KIHestad/Ctrl-MC/Prototype2/SRC/DisplayHeadUnit_ESP32/README.md

Ctrl-MC logo

# Arduino Motorcycle Controller Software - PROTOTYPE 2

This is the second prototype from September 2025, for use with ESP32 WROOM 32 dev board. 
It is just for testing how to create a speedomenter and tachometer (rpm counter) using different kind of sensors.

Check here for more info: https://youtu.be/J_AsExU7qkA?si=yqhxXnDfag6Xr95b
