KIHestad/Ctrl-MC/Documents/Marketing Images/Keyboard_ver1.png

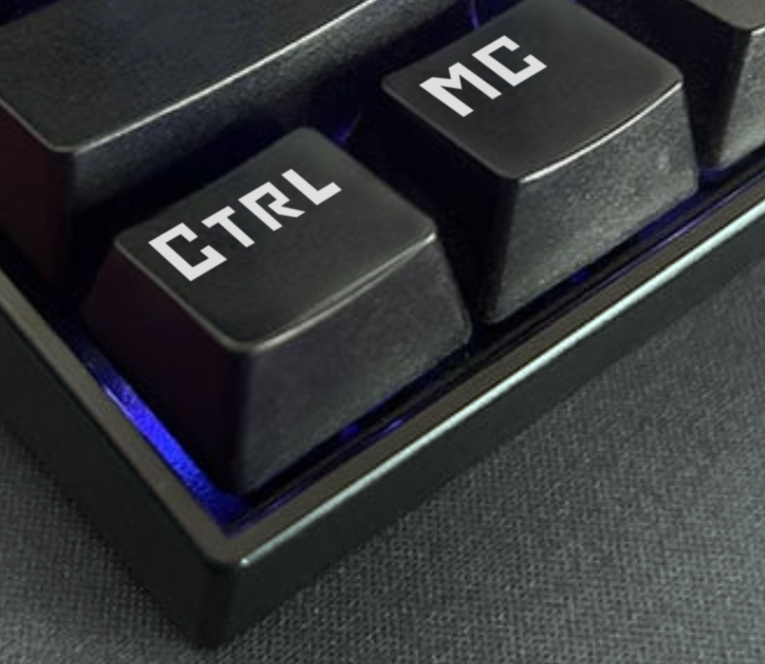
Documents/Marketing Images/Keyboard_ver1.png
