KIHestad/Ctrl-MC/Prototype4_8ch_spoc/Prototype4_8ch_spoc_SRC/_documents/documents/infineon-spoc-bts72220-4esa-datasheet-figure_37.png

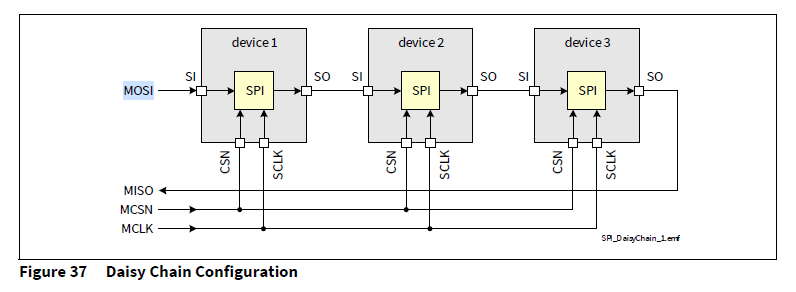
Prototype4_8ch_spoc/Prototype4_8ch_spoc_SRC/_documents/documents/infineon-spoc-bts72220-4esa-datasheet-figure_37.png
