KIHestad/Ctrl-MC/Prototype4_8ch_spoc/Prototype4_8ch_spoc_SRC/_documents/documents/infineon-spoc-bts72220-4esa-datasheet-figure_38.png

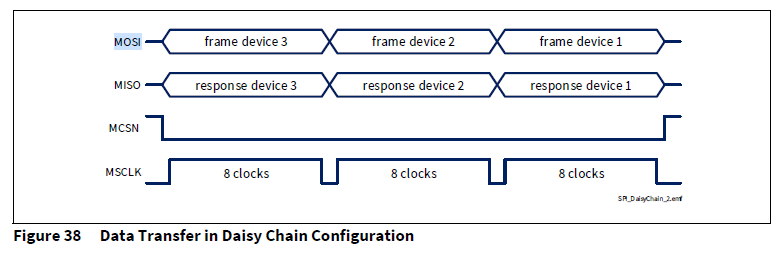
Prototype4_8ch_spoc/Prototype4_8ch_spoc_SRC/_documents/documents/infineon-spoc-bts72220-4esa-datasheet-figure_38.png
