KIHestad/Ctrl-MC/Ctrl-MC_DisplayUnit/include/Image.h

/***  Ctrl-MC // An open source Motorcycle Controller Arduino project by KI Hestad: https://github.com/KIHestad/Ctrl-MC  ***/

class Image {

    private:

        void image(const unsigned char img[], ImagePosition imgPos, uint8_t width, uint8_t height) {
            if (imgPos == imgPosMenuCenter)
                display.drawBitmap((DISPLAY_SCREEN_WIDTH/2)-(width/2), 3+25-(height/2), img, width, height, SSD1306_WHITE);
            else if (imgPos == imgPosCenter)
                display.drawBitmap((DISPLAY_SCREEN_WIDTH/2)-(width/2), (DISPLAY_SCREEN_HEIGHT/2)-(height/2), img, width, height, SSD1306_WHITE);
            else if (imgPos == imgPos2Left)
                display.drawBitmap(0, (DISPLAY_SCREEN_HEIGHT/2)-(height/2), img, width, height, SSD1306_WHITE);
            else if (imgPos == imgPos2Right)
                display.drawBitmap(DISPLAY_SCREEN_WIDTH-width, (DISPLAY_SCREEN_HEIGHT/2)-(height/2), img, width, height, SSD1306_WHITE);
            else if (imgPos == imgPos3Left)
                display.drawBitmap(((DISPLAY_SCREEN_WIDTH-35)/2)-(width/2), (DISPLAY_SCREEN_HEIGHT/2)-(height/2), img, width, height, SSD1306_WHITE);
            else if (imgPos == imgPos3RightTop)
                display.drawBitmap(DISPLAY_SCREEN_WIDTH-width, 0, img, width, height, SSD1306_WHITE);
            else if (imgPos == imgPos3RightBottom)
                display.drawBitmap(DISPLAY_SCREEN_WIDTH-width, DISPLAY_SCREEN_HEIGHT/2, img, width, height, SSD1306_WHITE);
        }

    public:
    
        void kiHestadLogo() {
            static const unsigned char PROGMEM img[] = {
                0xff, 0xff, 0xff, 0xff, 0xff, 0xff, 0xff, 0xff, 0xff, 0xff, 0xff, 0xff, 0xff, 0xff, 0xff, 0xff, 
                0xff, 0xff, 0xff, 0xff, 0xff, 0xff, 0xff, 0xff, 0xff, 0xff, 0xff, 0xff, 0xff, 0xff, 0xff, 0xff, 
                0xff, 0xff, 0xff, 0xff, 0xff, 0xff, 0xff, 0xff, 0xff, 0xff, 0xff, 0xff, 0xff, 0xff, 0xff, 0xff, 
                0xff, 0xff, 0xff, 0xff, 0xff, 0xff, 0xff, 0xe0, 0x07, 0xff, 0xff, 0xff, 0xff, 0xff, 0xff, 0xff, 
                0xff, 0xff, 0xff, 0xff, 0xff, 0xff, 0xfe, 0x00, 0x00, 0x7f, 0xff, 0xff, 0xff, 0xff, 0xff, 0xff, 
                0xff, 0xff, 0xff, 0xff, 0xff, 0xff, 0xf0, 0x1f, 0xf8, 0x1f, 0xff, 0xff, 0xff, 0xff, 0xff, 0xff, 
                0xff, 0xff, 0xff, 0xff, 0xff, 0xff, 0xc1, 0xff, 0xff, 0x03, 0xff, 0xff, 0xff, 0xff, 0xff, 0xff, 
                0xff, 0xff, 0xff, 0xff, 0xff, 0xff, 0x87, 0xdf, 0xff, 0xe1, 0xff, 0xff, 0xff, 0xff, 0xff, 0xff, 
                0xff, 0xff, 0xff, 0xff, 0xff, 0xfe, 0x1f, 0x8f, 0x3d, 0xf8, 0x7f, 0xff, 0xff, 0xff, 0xff, 0xff, 
                0xff, 0xff, 0xff, 0xff, 0xff, 0xfc, 0x7d, 0xcf, 0x3c, 0xfe, 0x3f, 0xff, 0xff, 0xff, 0xff, 0xff, 
                0xff, 0xff, 0xff, 0xff, 0xff, 0xf8, 0xf8, 0xc6, 0x38, 0xff, 0x1f, 0xff, 0xff, 0xff, 0xff, 0xff, 
                0xff, 0xff, 0xff, 0xff, 0xff, 0xf3, 0xfc, 0x42, 0x11, 0xcf, 0x8f, 0xff, 0xff, 0xff, 0xff, 0xff, 
                0xff, 0xff, 0xff, 0xff, 0xff, 0xe7, 0xfc, 0x00, 0x00, 0x8f, 0xc7, 0xff, 0xff, 0xff, 0xff, 0xff, 
                0xff, 0xff, 0xff, 0xff, 0xff, 0xcf, 0xfc, 0x0c, 0xc4, 0x0f, 0xe3, 0xff, 0xff, 0xff, 0xff, 0xff, 
                0xff, 0xff, 0xff, 0xff, 0xff, 0x9f, 0xfc, 0x7f, 0xfc, 0x0f, 0xf1, 0xff, 0xff, 0xff, 0xff, 0xff, 
                0xff, 0xff, 0xff, 0xff, 0xff, 0x1f, 0xfe, 0x7f, 0xff, 0xcf, 0xf8, 0xff, 0xff, 0xff, 0xff, 0xff, 
                0xff, 0xff, 0xff, 0xff, 0xff, 0x3f, 0xfe, 0xff, 0xff, 0xcf, 0xfc, 0xff, 0xff, 0xff, 0xff, 0xff, 
                0xff, 0xff, 0xff, 0xff, 0xfe, 0x7f, 0xff, 0xff, 0xff, 0xff, 0xfe, 0x7f, 0xff, 0xff, 0xff, 0xff, 
                0xff, 0xff, 0xff, 0xff, 0xfc, 0x7f, 0xf1, 0xff, 0xff, 0xef, 0xfe, 0x7f, 0xff, 0xff, 0xff, 0xff, 
                0xff, 0xff, 0xff, 0xff, 0xfc, 0xff, 0xe0, 0xff, 0xff, 0xc3, 0xff, 0x3f, 0xff, 0xff, 0xff, 0xff, 
                0xff, 0xff, 0xff, 0xff, 0xf8, 0xff, 0xe4, 0xff, 0xbf, 0xc3, 0xff, 0x3f, 0xff, 0xff, 0xff, 0xff, 
                0xff, 0xff, 0xff, 0xff, 0xf9, 0xff, 0xe7, 0xf1, 0x87, 0xf3, 0xff, 0x9f, 0xff, 0xff, 0xff, 0xff, 
                0xff, 0xff, 0xff, 0xff, 0xf9, 0xff, 0xe7, 0xc3, 0xc3, 0xf9, 0xff, 0x9f, 0xff, 0xff, 0xff, 0xff, 
                0xff, 0xff, 0xff, 0xff, 0xf3, 0xff, 0xe7, 0x8f, 0xf3, 0xf9, 0xff, 0x9f, 0xff, 0xff, 0xff, 0xff, 
                0xff, 0xff, 0xff, 0xff, 0xf3, 0xff, 0xe7, 0xff, 0xff, 0x93, 0xff, 0xcf, 0xff, 0xff, 0xff, 0xff, 
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
                0x00, 0x00, 0x00, 0x00, 0x00, 0x00, 0x00, 0x00, 0x00, 0x00, 0x00, 0x00, 0x00, 0x00
            };
            uint8_t width = 50;
            uint8_t height = 50;
            if (left) {
                uint8_t leftPosition = (DISPLAY_SCREEN_WIDTH/2)-6-width;
                display.drawBitmap(leftPosition, 3, img, width, height, SSD1306_INVERSE);
            } 
            if (right) {
                uint8_t leftPosition = (DISPLAY_SCREEN_WIDTH/2)+6;
                display.drawBitmap(leftPosition, 3, img, width, height, SSD1306_INVERSE);
            } 

        }
        
        void menuSelectIconConfirm(bool left, bool right) {
            static const unsigned char PROGMEM img[] = {
                // 'MenuCheckIconX', 19x19px
                0x20, 0x00, 0x80, 0x70, 0x01, 0xc0, 0xf8, 0x03, 0xe0, 0x7c, 0x07, 0xc0, 0x3e, 0x0f, 0x80, 0x1f, 
                0x1f, 0x00, 0x0f, 0xbe, 0x00, 0x07, 0xfc, 0x00, 0x03, 0xf8, 0x00, 0x01, 0xf0, 0x00, 0x03, 0xf8, 
                0x00, 0x07, 0xfc, 0x00, 0x0f, 0xbe, 0x00, 0x1f, 0x1f, 0x00, 0x3e, 0x0f, 0x80, 0x7c, 0x07, 0xc0, 
                0xf8, 0x03, 0xe0, 0x70, 0x01, 0xc0, 0x20, 0x00, 0x80
            };
            uint8_t width = 19;
            uint8_t height = 19;
            uint8_t y = 3 + 11;
            if (left) {
                uint8_t x = ((DISPLAY_SCREEN_WIDTH/2)-6-25)-(width/2);
                display.drawBitmap(x, y, img, width, height, SSD1306_WHITE);
            }
            if (right) {
                uint8_t x = ((DISPLAY_SCREEN_WIDTH/2)+6+25)-(width/2);
                display.drawBitmap(x, y, img, width, height, SSD1306_WHITE);
            }

        }

        void menuSelectIconReject(bool left, bool right) {
            static const unsigned char PROGMEM img[] = {
                // 'MenuCheckIconCheck', 19x18px
                0x00, 0x00, 0x80, 0x00, 0x01, 0xc0, 0x00, 0x03, 0xe0, 0x00, 0x03, 0xe0, 0x00, 0x07, 0xc0, 0x00, 
                0x0f, 0x80, 0x00, 0x1f, 0x00, 0x00, 0x1f, 0x00, 0x00, 0x3e, 0x00, 0x20, 0x7c, 0x00, 0x70, 0xf8, 
                0x00, 0xf8, 0xf8, 0x00, 0x7d, 0xf0, 0x00, 0x3f, 0xe0, 0x00, 0x1f, 0xc0, 0x00, 0x0f, 0xc0, 0x00, 
                0x07, 0x80, 0x00, 0x03, 0x00, 0x00
            };
            uint8_t width = 19;
            uint8_t height = 18;
            uint8_t y = 3 + 11;
            if (left) {
                uint8_t x = ((DISPLAY_SCREEN_WIDTH/2)-6-25)-(width/2);
                display.drawBitmap(x, y, img, width, height, SSD1306_WHITE);
            }
            if (right) {
                uint8_t x = ((DISPLAY_SCREEN_WIDTH/2)+6+25)-(width/2);
                display.drawBitmap(x, y, img, width, height, SSD1306_WHITE);
            }

        }

        void menuSelectIconOn(bool left, bool right) {
            static const unsigned char PROGMEM img[] = {
                // 'MenuCheckOn', 30x32px
                0x00, 0x07, 0x80, 0x00, 0x00, 0x07, 0x80, 0x00, 0x00, 0x07, 0x80, 0x00, 0x00, 0x67, 0x98, 0x00, 
                0x01, 0xe7, 0x9e, 0x00, 0x03, 0xe7, 0x9f, 0x00, 0x0f, 0xe7, 0x9f, 0xc0, 0x0f, 0xc7, 0x8f, 0xe0, 
                0x1f, 0x07, 0x83, 0xe0, 0x3e, 0x07, 0x81, 0xf0, 0x3c, 0x07, 0x80, 0xf0, 0x7c, 0x07, 0x80, 0xf8, 
                0x78, 0x07, 0x80, 0x78, 0xf8, 0x07, 0x80, 0x7c, 0xf0, 0x07, 0x80, 0x3c, 0xf0, 0x07, 0x80, 0x3c, 
                0xf0, 0x07, 0x80, 0x3c, 0xf0, 0x00, 0x00, 0x3c, 0xf0, 0x00, 0x00, 0x3c, 0xf0, 0x00, 0x00, 0x3c, 
                0xf8, 0x00, 0x00, 0x7c, 0x78, 0x00, 0x00, 0x78, 0x7c, 0x00, 0x00, 0xf8, 0x3c, 0x00, 0x00, 0xf0, 
                0x3e, 0x00, 0x01, 0xf0, 0x1f, 0x00, 0x03, 0xe0, 0x1f, 0xc0, 0x0f, 0xe0, 0x0f, 0xf0, 0x3f, 0xc0, 
                0x07, 0xff, 0xff, 0x80, 0x01, 0xff, 0xfe, 0x00, 0x00, 0x7f, 0xf8, 0x00, 0x00, 0x1f, 0xe0, 0x00
            };
            uint8_t width = 30;
            uint8_t height = 32;
            uint8_t y = 3 + (50/2) - (height/2); // (50/2) = Middle of Checkbox frama size
            if (left) {
                uint8_t x = (DISPLAY_SCREEN_WIDTH/2)-6-(50/2)-(width/2); // (50/2) = Middle of Checkbox frama size
                display.drawBitmap(x, y, img, width, height, SSD1306_WHITE);
            } 
            if (right) {
                uint8_t x = (DISPLAY_SCREEN_WIDTH/2)+6+(50/2)-(width/2); // (50/2) = Middle of Checkbox frama size 
                display.drawBitmap(x, y, img, width, height, SSD1306_WHITE);
            } 

        }

        void menuSelectIconOff(bool left, bool right) {
            static const unsigned char PROGMEM img[] = {
                // 'MenuCheckOff', 30x32px
                0x00, 0x00, 0x00, 0x00, 0x00, 0x1f, 0xe0, 0x00, 0x18, 0x7f, 0xf8, 0x00, 0x3c, 0x7f, 0xfe, 0x00, 
                0x7e, 0x3f, 0xff, 0x00, 0x3f, 0x10, 0x3f, 0xc0, 0x1f, 0x80, 0x0f, 0xe0, 0x0f, 0xc0, 0x03, 0xe0, 
                0x07, 0xe0, 0x01, 0xf0, 0x23, 0xf0, 0x00, 0xf0, 0x71, 0xf8, 0x00, 0xf8, 0x78, 0xfc, 0x00, 0x78, 
                0xf8, 0x7e, 0x00, 0x7c, 0xf0, 0x3f, 0x00, 0x3c, 0xf0, 0x1f, 0x80, 0x3c, 0xf0, 0x0f, 0x00, 0x3c, 
                0xf0, 0x06, 0x00, 0x3c, 0xf0, 0x00, 0x00, 0x3c, 0xf0, 0x00, 0x00, 0x3c, 0xf8, 0x00, 0x00, 0x7c, 
                0x78, 0x00, 0x00, 0x78, 0x7c, 0x00, 0x00, 0xf8, 0x3c, 0x00, 0x00, 0xf0, 0x3e, 0x00, 0x01, 0xf0, 
                0x1f, 0x00, 0x03, 0xe0, 0x1f, 0xc0, 0x0f, 0xe0, 0x0f, 0xf0, 0x3f, 0xc0, 0x07, 0xff, 0xff, 0x80, 
                0x01, 0xff, 0xfe, 0x00, 0x00, 0x7f, 0xf8, 0x00, 0x00, 0x1f, 0xe0, 0x00, 0x00, 0x00, 0x00, 0x00
            };
            uint8_t width = 30;
            uint8_t height = 32;
            uint8_t y = 3 + (50/2) - (height/2); // (50/2) = Middle of Checkbox frama size
            if (left) {
                uint8_t x = (DISPLAY_SCREEN_WIDTH/2)-6-(50/2)-(width/2); // (50/2) = Middle of Checkbox frama size
                display.drawBitmap(x, y, img, width, height, SSD1306_WHITE);
            } 
            if (right) {
                uint8_t x = (DISPLAY_SCREEN_WIDTH/2)+6+(50/2)-(width/2); // (50/2) = Middle of Checkbox frama size 
                display.drawBitmap(x, y, img, width, height, SSD1306_WHITE);
            } 

        }

};
