KIHestad/Ctrl-MC/Prototype4_8ch_spoc/Prototype4_8ch_spoc_SRC/Core/Src/feature/cmc_feature_direction_indicator.c

/**
  *********************************************************************************************
  * @file      cmc_feature_direction_indicator.c
  * @brief     Direction indicator (turn signal) feature — manages left, right and hazard blinking
  * @details   Manages the direction indicator state based on the turn signal button inputs and configuration
  * @attention This is part of the Ctrl-MC system: https://github.com/KIHestad/Ctrl-MC
  * @copyright KI Hestad, Complicated Productions
  *********************************************************************************************
  */

#include "config/cmc_config_type_unit.h"
#include "stm32g4xx_hal.h"
#include "config/cmc_config_type.h"
#include "app/cmc_app_state.h"
#include "can/cmc_can_manager.h"
#include "can/cmc_can_message.h"
#include "feature/cmc_features_manager.h"
#include "feature/cmc_features_output.h"
#include "input/cmc_input.h"
#include <stdint.h>
#include "feature/cmc_feature_test_channels.h"
#include "feature/cmc_feature_direction_indicator.h"

// Locals
// Static variables to track the horn state and configuration on this unit
static bool feature_enabled               = false;   // Cached in init(): enabled config-wide AND not test-mode-suppressed; gates state resolution (hazard/cancel-other), regardless of local outputs
static bool this_unit_feature_out_enabled = false;   // True if the feature is enabled and at least one relevant output exists on this unit
static uint8_t switches_left_count        = 0;       // The number of output channels for the left direction indicator on this unit
static uint8_t switches_right_count       = 0;       // The number of output channels for the right direction indicator on this unit
static uint8_t switch_left_id[5]          = {0xFF, 0xFF, 0xFF, 0xFF, 0xFF};    // The output indexes for the left direction indicator on this unit
static uint8_t switch_right_id[5]         = {0xFF, 0xFF, 0xFF, 0xFF, 0xFF};    // The output indexes for the right direction indicator on this unit

// Active state tracking for the direction indicator
static bool this_unit_left_active         = false;   // True if the left direction indicator is currently active (output on)
static bool this_unit_right_active        = false;   // True if the right direction indicator is currently active (output on)
static uint32_t interval_speed_ms         = 500;     // Blinking interval in milliseconds, not configurable for now
static uint32_t on_since_ms               = 0;       // Tick at which the direction indicator was last turned on, used for auto shut-off timeout

// Blink phase sync
static uint32_t blink_epoch_ms            = 0U;      // Tick captured at activation; phase is relative to this so all units start aligned
static bool     is_originator             = false;   // True when the active indication was started by the local button on this unit
static uint32_t last_resync_ms            = 0U;      // Last tick at which the originator sent a periodic resync broadcast
#define CMC_FEATURE_DI_RESYNC_INTERVAL_MS 3600000U   // Re-broadcast every 1 hour to correct long-term crystal drift on slave units

// State machine edge tracking — prev_app tracks the last seen app_state values for self-detecting change detection
static bool     prev_app_left           = false;     // last seen app_state left_on
static bool     prev_app_right          = false;     // last seen app_state right_on
static uint32_t left_activated_ms       = 0U;        // tick when left was last activated (hazard window)
static uint32_t right_activated_ms      = 0U;        // tick when right was last activated (hazard window)
#define CMC_FEATURE_DI_HAZARD_WINDOW_MS 400U         // both buttons within this window → hazard

// Sync the cancelled side: write false back to app_state, update prev_app, and reset the scanner
// toggle so the very next physical press acts as "turn on" (no dead press required).
static void cancel_left(void) {
    cmc_app_state.feature.directional_indicator.left_on = false;
    prev_app_left = false;
    cmc_input_scanner_reset_toggle_by_device(CMC_CONFIG_IN_DEVICE_TURN_LEFT);
}
static void cancel_right(void) {
    cmc_app_state.feature.directional_indicator.right_on = false;
    prev_app_right = false;
    cmc_input_scanner_reset_toggle_by_device(CMC_CONFIG_IN_DEVICE_TURN_RIGHT);
}

static void set_switch_left(bool on, bool update_active_state) {
    for (uint8_t i = 0; i < switches_left_count; i++) {
        cmc_features_out_set_switch(switch_left_id[i], on);
    }
    if (update_active_state) { 
        this_unit_left_active = on;
     }
}

static void set_switch_right(bool on, bool update_active_state) {
    for (uint8_t i = 0; i < switches_right_count; i++) {
        cmc_features_out_set_switch(switch_right_id[i], on);
    }
    if (update_active_state) { 
        this_unit_right_active = on;
     }
}

static void cmc_feature_direction_indicator_broadcast()
{
    // Broadcast over CAN so other units update their cmc_app_state
    struct cmc_can_message_feature_direction_indicator_t di_msg;
    bool hazard = this_unit_left_active && this_unit_right_active;
    di_msg.turn_signal_on          = (this_unit_left_active || this_unit_right_active) ? 1U : 0U;
    di_msg.turn_signal_direction = hazard ? 2U : (this_unit_right_active ? 1U : 0U);
    di_msg.turn_signal_position = 2U; // both front and rear
    di_msg.dashboard_only  = 0U; // normal operation
    uint8_t di_payload[CMC_CAN_MESSAGE_FEATURE_DIRECTION_INDICATOR_LENGTH];
    if (cmc_can_message_feature_direction_indicator_pack(di_payload, &di_msg, sizeof(di_payload)) < 0) { return; }
    cmc_can_manager_send(CMC_CAN_MESSAGE_FEATURE_DIRECTION_INDICATOR_FRAME_ID, di_payload, CMC_CAN_MESSAGE_FEATURE_DIRECTION_INDICATOR_LENGTH);
}

void cmc_feature_direction_indicator_init(void)
{
    // if not this feature is active, do nothing
    feature_enabled = (cmc_config.feature_direction_indicator.enabled == 1) &&
        !cmc_feature_test_channels_suppresses(cmc_config.feature_direction_indicator.enabled_on_test);
    if (!feature_enabled) {
       return;
    }
    
    // Check if any outputs are active, could be multiple - first left (+ common)
    if (cmc_features_out_is_device_enabled(CMC_CONFIG_OUT_DEVICE_TURN_LEFT_ALL)) {
        switch_left_id[switches_left_count++] = cmc_features_out_get_device_id(CMC_CONFIG_OUT_DEVICE_TURN_LEFT_ALL);
    }
    if (cmc_features_out_is_device_enabled(CMC_CONFIG_OUT_DEVICE_TURN_LEFT_FRONT)) {
        switch_left_id[switches_left_count++] = cmc_features_out_get_device_id(CMC_CONFIG_OUT_DEVICE_TURN_LEFT_FRONT);
    }
    if (cmc_features_out_is_device_enabled(CMC_CONFIG_OUT_DEVICE_TURN_LEFT_REAR)) {
        switch_left_id[switches_left_count++] = cmc_features_out_get_device_id(CMC_CONFIG_OUT_DEVICE_TURN_LEFT_REAR);
    }
    if (cmc_features_out_is_device_enabled(CMC_CONFIG_OUT_DEVICE_INSTR_TURN_LEFT)) {
        switch_left_id[switches_left_count++] = cmc_features_out_get_device_id(CMC_CONFIG_OUT_DEVICE_INSTR_TURN_LEFT);
    }
    if (cmc_features_out_is_device_enabled(CMC_CONFIG_OUT_DEVICE_INSTR_TURN_COMMON)) {
        switch_left_id[switches_left_count++] = cmc_features_out_get_device_id(CMC_CONFIG_OUT_DEVICE_INSTR_TURN_COMMON);
    }
    // Check if any outputs are active, could be multiple - now right (+ common)
    if (cmc_features_out_is_device_enabled(CMC_CONFIG_OUT_DEVICE_TURN_RIGHT_ALL)) {
        switch_right_id[switches_right_count++] = cmc_features_out_get_device_id(CMC_CONFIG_OUT_DEVICE_TURN_RIGHT_ALL);
    }
    if (cmc_features_out_is_device_enabled(CMC_CONFIG_OUT_DEVICE_TURN_RIGHT_FRONT)) {
        switch_right_id[switches_right_count++] = cmc_features_out_get_device_id(CMC_CONFIG_OUT_DEVICE_TURN_RIGHT_FRONT);
    }
    if (cmc_features_out_is_device_enabled(CMC_CONFIG_OUT_DEVICE_TURN_RIGHT_REAR)) {
        switch_right_id[switches_right_count++] = cmc_features_out_get_device_id(CMC_CONFIG_OUT_DEVICE_TURN_RIGHT_REAR);
    }
    if (cmc_features_out_is_device_enabled(CMC_CONFIG_OUT_DEVICE_INSTR_TURN_RIGHT)) {
        switch_right_id[switches_right_count++] = cmc_features_out_get_device_id(CMC_CONFIG_OUT_DEVICE_INSTR_TURN_RIGHT);
    }
    if (cmc_features_out_is_device_enabled(CMC_CONFIG_OUT_DEVICE_INSTR_TURN_COMMON)) {
        switch_right_id[switches_right_count++] = cmc_features_out_get_device_id(CMC_CONFIG_OUT_DEVICE_INSTR_TURN_COMMON);
    }
    // If at least one output is enabled, the feature is active
    this_unit_feature_out_enabled = (switches_left_count > 0) || (switches_right_count > 0);
    // Continue if still active    
    if (this_unit_feature_out_enabled) {
        // Ensure the direction indicators start in the off state on initialization
        set_switch_left(false, true);
        set_switch_right(false, true);
        // Get blinking speed from config, use default if out of range
        if (cmc_config.feature_direction_indicator.blink_interval_x10ms >= 10 && 
            cmc_config.feature_direction_indicator.blink_interval_x10ms <= 200) {
            interval_speed_ms = (uint32_t)cmc_config.feature_direction_indicator.blink_interval_x10ms * 10U;
        }
    }
    // Seed prev_app from current app_state so the first process() call does not fire spuriously
    prev_app_left  = cmc_app_state.feature.directional_indicator.left_on;
    prev_app_right = cmc_app_state.feature.directional_indicator.right_on;
}

void cmc_feature_direction_indicator_process(void)
{
    // Must be checked here too, not just in init(): the hazard/cancel-other state machine below
    // runs unconditionally otherwise, resetting the scanner's raw button toggle state (via
    // cancel_left/cancel_right) even when this feature is disabled or test-mode-suppressed.
    // Uses the cached flag from init() rather than re-reading config every tick.
    if (!feature_enabled) {
        return;
    }

    // Get current app state for the directional indicator inputs (buttons), and track if we're in hazard mode (both on)
    bool cur_left  = cmc_app_state.feature.directional_indicator.left_on;
    bool cur_right = cmc_app_state.feature.directional_indicator.right_on;
    bool in_hazard = this_unit_left_active && this_unit_right_active;

    // Check for auto shut-off (not applied during hazard)
    if (on_since_ms > 0U && cmc_config.feature_direction_indicator.auto_shut_off_sec > 0U && !in_hazard && (cur_left || cur_right)) {
        if ((HAL_GetTick() - on_since_ms) >= ((uint32_t)cmc_config.feature_direction_indicator.auto_shut_off_sec * 1000U)) {
            set_switch_left(false, true);
            set_switch_right(false, true);
            cancel_left();
            cancel_right();
            on_since_ms = 0U;
            cmc_feature_direction_indicator_broadcast();
            return;
        }
    } else {
        on_since_ms = 0U;        
    }

    if (cur_left != prev_app_left || cur_right != prev_app_right) {

        bool just_left_on   =  cur_left  && !prev_app_left;
        bool just_right_on  =  cur_right && !prev_app_right;
        bool just_left_off  = !cur_left  &&  prev_app_left;
        bool just_right_off = !cur_right &&  prev_app_right;

        prev_app_left  = cur_left;
        prev_app_right = cur_right;

        bool new_left  = this_unit_left_active;   // default: keep current
        bool new_right = this_unit_right_active;


        if (just_left_on && just_right_on) {
            // Both toggled on in the same tick → hazard
            new_left = true;  new_right = true;
        } else if (in_hazard && (just_left_off || just_right_off)) {
            // Either side released while in hazard → cancel all
            new_left = false; new_right = false;
        } else if (just_right_on && this_unit_left_active && !this_unit_right_active) {
            // Right pressed while left is active: hazard if within window, else cancel-other
            if ((HAL_GetTick() - left_activated_ms) <= CMC_FEATURE_DI_HAZARD_WINDOW_MS) {
                new_left = true;  new_right = true;
            } else {
                new_left = false; new_right = true;
            }
        } else if (just_left_on && this_unit_right_active && !this_unit_left_active) {
            // Left pressed while right is active: hazard if within window, else cancel-other
            if ((HAL_GetTick() - right_activated_ms) <= CMC_FEATURE_DI_HAZARD_WINDOW_MS) {
                new_left = true;  new_right = true;
            } else {
                new_left = true;  new_right = false;
            }
        } else if (just_left_on)  { new_left  = true;  }
        else if (just_left_off)   { new_left  = false; }
        else if (just_right_on)   { new_right = true;  }
        else if (just_right_off)  { new_right = false; }

        // Track activation timestamps for hazard window, auto shut-off, and blink phase sync
        if (new_left  && !this_unit_left_active)  { left_activated_ms  = HAL_GetTick(); on_since_ms = HAL_GetTick(); blink_epoch_ms = HAL_GetTick(); }
        if (new_right && !this_unit_right_active) { right_activated_ms = HAL_GetTick(); on_since_ms = HAL_GetTick(); blink_epoch_ms = HAL_GetTick(); }

        // Apply resolved active state and turn off outputs if deactivated.
        // cancel_left/right also resets the scanner toggle so the next press immediately activates.
        if (!new_left  && this_unit_left_active)  { set_switch_left(false, true);  cancel_left(); }
        if (!new_right && this_unit_right_active) { set_switch_right(false, true); cancel_right(); }
        this_unit_left_active  = new_left;
        this_unit_right_active = new_right;

        // Only TX over CAN if the change originated from the local input scanner
        if (cmc_app_state.feature.directional_indicator.pending_broadcast) {
            cmc_app_state.feature.directional_indicator.pending_broadcast = false;
            // Track whether this unit is the originator so it can do periodic resync broadcasts
            is_originator = (new_left || new_right);
            if (is_originator) { last_resync_ms = HAL_GetTick(); }
            cmc_feature_direction_indicator_broadcast();
        }
    }

    // ---- Output: only runs on units that have physical turn signal outputs ----
    if (!this_unit_feature_out_enabled) { return; }
    if (!this_unit_left_active && !this_unit_right_active) { return; }

    // Re-anchor blink epoch when a resync signal arrives from the originator via CAN (slave path)
    if (cmc_app_state.feature.directional_indicator.pending_resync) {
        cmc_app_state.feature.directional_indicator.pending_resync = false;
        blink_epoch_ms = HAL_GetTick();
    }

    // Originator only: re-broadcast every CMC_FEATURE_DI_RESYNC_INTERVAL_MS so slave units
    // re-anchor their epoch and eliminate long-term crystal drift
    if (is_originator && (HAL_GetTick() - last_resync_ms) >= CMC_FEATURE_DI_RESYNC_INTERVAL_MS) {
        last_resync_ms = HAL_GetTick();
        blink_epoch_ms = HAL_GetTick();
        cmc_feature_direction_indicator_broadcast();
    }

    // Blink: drive outputs on/off based on phase relative to epoch (not absolute tick) so all
    // units start in phase on activation and stay aligned after periodic resync broadcasts
    bool phase_on = (((HAL_GetTick() - blink_epoch_ms) / interval_speed_ms) & 1U) == 0U;
    if (this_unit_left_active)  { set_switch_left(phase_on,  false); }
    if (this_unit_right_active) { set_switch_right(phase_on, false); }
}
