KIHestad/Ctrl-MC/Prototype4_8ch_spoc/Prototype4_8ch_spoc_SRC/Core/Src/feature/cmc_feature_ignition.c

/**
  *********************************************************************************************
  * @file      cmc_feature_ignition.c
  * @brief     Ignition feature control logic
  * @details   Controls cmc_app_state.veichle_state.ignition_on based on configuration:
  *            - Disabled (enabled=0): ignition_on is forced to true unconditionally.
  *              Use when no ignition sensor is wired or during bench testing.
  *            - Enabled (enabled=1): ignition_on starts false, then follows the
  *              CMC_CONFIG_IN_DEVICE_IGNITION input pin (active-low: LOW = ignition on)
  *              via cmc_app_state_update() on this unit, and is broadcast over CAN on change.
  *              Other units receive the state via CMC_CAN_MESSAGE_FEATURE_IGNITION_FRAME_ID.
  * @attention This is part of the Ctrl-MC system: https://github.com/KIHestad/Ctrl-MC
  * @copyright KI Hestad, Complicated Productions
  *********************************************************************************************
  */

#include "stm32g4xx_hal.h"
#include "config/cmc_config_type.h"
#include "app/cmc_app_state.h"
#include "can/cmc_can_manager.h"
#include "can/cmc_can_message.h"
#include "feature/cmc_feature_test_channels.h"
#include "feature/cmc_feature_ignition.h"

static bool feature_enabled = false; // Cached from config in init to avoid repeated reads

static void cmc_feature_ignition_broadcast(void)
{
    struct cmc_can_message_feature_ignition_t msg;
    msg.ignition_on = cmc_app_state.vehicle.ignition_on ? 1U : 0U;
    uint8_t payload[CMC_CAN_MESSAGE_FEATURE_IGNITION_LENGTH];
    if (cmc_can_message_feature_ignition_pack(payload, &msg, sizeof(payload)) < 0) { return; }
    cmc_can_manager_send(CMC_CAN_MESSAGE_FEATURE_IGNITION_FRAME_ID, payload, CMC_CAN_MESSAGE_FEATURE_IGNITION_LENGTH);
}

void cmc_feature_ignition_init(void) {
    feature_enabled = (cmc_config.feature_ignition.enabled == 1) &&
        !cmc_feature_test_channels_suppresses(cmc_config.feature_ignition.enabled_on_test);
    if (!feature_enabled) {
        // Disabled: force ignition on — no hardware dependency required
        cmc_app_state.vehicle.ignition_on = true;
    } else {
        // Enabled: start as off; the scanner will drive it on via cmc_app_state_update
        // when CMC_CONFIG_IN_DEVICE_IGNITION is configured and the pin is active (LOW)
        cmc_app_state.vehicle.ignition_on = false;
    }
}

void cmc_feature_ignition_process(void) {
    if (!feature_enabled) {
        // Disabled: keep forcing ignition on each loop so no other source can override
        cmc_app_state.vehicle.ignition_on = true;
    }
    // Broadcast if the ignition state changed (only on the unit that has the ignition input)
    if (cmc_app_state.vehicle.ignition_on_pending_broadcast) {
        cmc_app_state.vehicle.ignition_on_pending_broadcast = false;
        cmc_feature_ignition_broadcast();
    }
}
