KIHestad/Ctrl-MC/Prototype4/Prototype4_SRC/Core/Inc/cmc_config_manager.h

/**
  *********************************************************************************************
  * @file      cmc_config_manager.h
  * @brief     Configuration manager for handling loading, validating, and saving system configuration
  * @attention This is part of the Ctrl-MC system: https://github.com/KIHestad/Ctrl-MC
  * @copyright KI Hestad, Complicated Productions
  *********************************************************************************************
  */

#ifndef CMC_CONFIG_MANAGER_H_
#define CMC_CONFIG_MANAGER_H_

#include "cmc_config_type.h"
#include <stdbool.h>

typedef enum {
    CMC_CONFIG_STATUS_SUCCESS = 0,
    CMC_CONFIG_STATUS_ERROR   = 1,
    CMC_CONFIG_STATUS_INVALID_FLASH_SIGNATURE = 2,
    CMC_CONFIG_STATUS_INVALID_RAM_SIGNATURE = 3,    
} cmc_config_status_t;

// Init
cmc_config_status_t cmc_config_manager_init(void);

// Manager methods
bool cmc_config_manager_is_valid_config(void);
cmc_config_status_t cmc_config_manager_validate(cmc_config_t* target_config);
cmc_config_status_t cmc_config_manager_save_to_flash(const cmc_config_t* new_config);
cmc_config_status_t cmc_config_manager_load_from_flash(cmc_config_t* target);

#endif /* CMC_CONFIG_MANAGER_H_ */
