KIHestad/Ctrl-MC/Ctrl-MC_HandlebarUnit/include/models.h

/***  Ctrl-MC // An open source Motorcycle Controller Arduino project by KI Hestad: https://github.com/KIHestad/Ctrl-MC  ***/

// System enums
enum TemperatureDefaultType { tempCelcius, tempFarenheit };
enum PinType {pinDigital, pinAnalog };
enum ChecBoxSelected { checkBoxLeft, checkBoxMid, checkBoxRight};
enum ImagePosition {imgPosMenuCenter, imgPosCenter, imgPos2Left, imgPos2Right, imgPos3Left, imgPos3RightTop, imgPos3RightBottom};

// Bike main status
enum BikeStatusIgnition { ignOff, ignPasswordMode, ignOn };
enum BikeStatusEngine { engStopped, engStartMotorEngaged, engUnknownStatus, engRunning };
enum BikeStatusLights { lightsOff, lightsPark, lightsMain };
enum BikeStatusLightsHiLo { lightsLow, lightsHigh };
enum BikeStatusIndicator { indOff, indLeft, indRight, indHazard };

class BikeStatus {
    public:

        bool debugMode; // Flag for running in debug mode
        
        bool handshakeOK; // Flag that indicates that communitcation to relay module is OK
        unsigned long handshakeNextTimestamp; // Timestamp for when next handshake should be triggered
        
        unsigned long ignitionOnTimestamp; // Set timestamp for when iginition was last turned on, used for stopwatch
        
        uint8_t displayMenyPageSelected; // The current page to show on display, selected by NEXT MENU ITEM button, 0=show status page
        uint8_t displayMenySubPageSelected; // The current submenu selected
        unsigned long displayMenuTimeoutTimestamp; // The timestamp in the future for set after each menu action to trigger automatically return to status page
        unsigned long displayMenyShowRunningStopWatch; // Set to actual time [millis()] to update time each second
        unsigned long displayGotoStatusPageTimestamp; // Timestamp for showing progressbar when goto status page was triggered
        bool displayGotoStatusPageProgress; // Flag set to true when progress goto status page is running 
        
        unsigned long indicatorNextBlinkTimestamp; // Timestamp for controller to know when to blink next time
        bool indicatorBlinkOn; // Flag to know to turn on or off turn signal, toggles for each ite
        bool neutral; // Flag set if bike gears in neutral position
        bool lightHighBeamFlash; // Flag set if hi/lo button is used as passing switch, set true when hi/lo button is pressed and holded for flashing with high beam

        BikeStatusIgnition ignition;
        BikeStatusEngine engine;
        BikeStatusLights lights;
        BikeStatusLightsHiLo lightHilo;
        BikeStatusIndicator indicator;
};

// Model for menu items
class MenuItem {
    public:
        uint8_t id; // Identifier used by code to know what to do
        String displayName; // Name of menu item to show on display
};

// Model for input pins
class Input {
    public:
        uint8_t pin; // pin number
        bool enabled; // enabled
};
